darshg321/FancyBoard/pcb/Choc_Stem_MX_Size_Normal.step

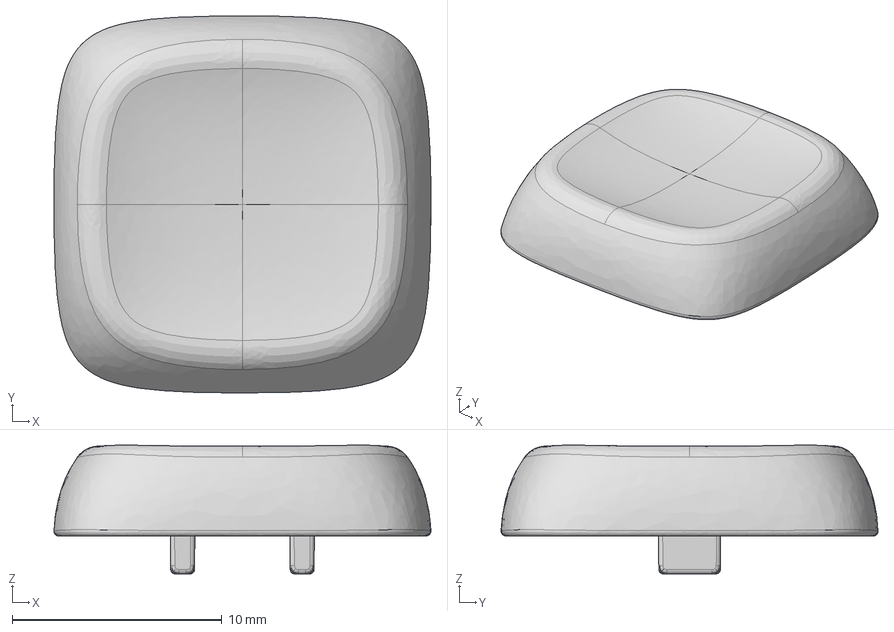
[picture p8: CAD file, 2025-07-31]
pcb/Choc_Stem_MX_Size_Normal.step
18.0 x 18.0 x 6.14 mm
