darshg321/FancyBoard/cad/draw1.dxf

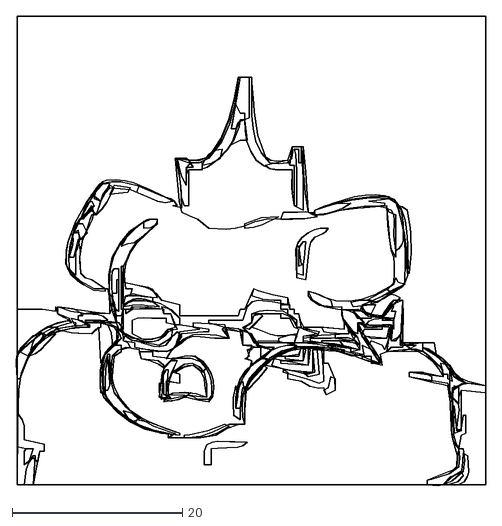
[picture p9: CAD file, 2025-08-01]
cad/draw1.dxf
55.2 x 55.1
