darshg321/FancyBoard/cad/keycaps/1.25u.SLDPRT

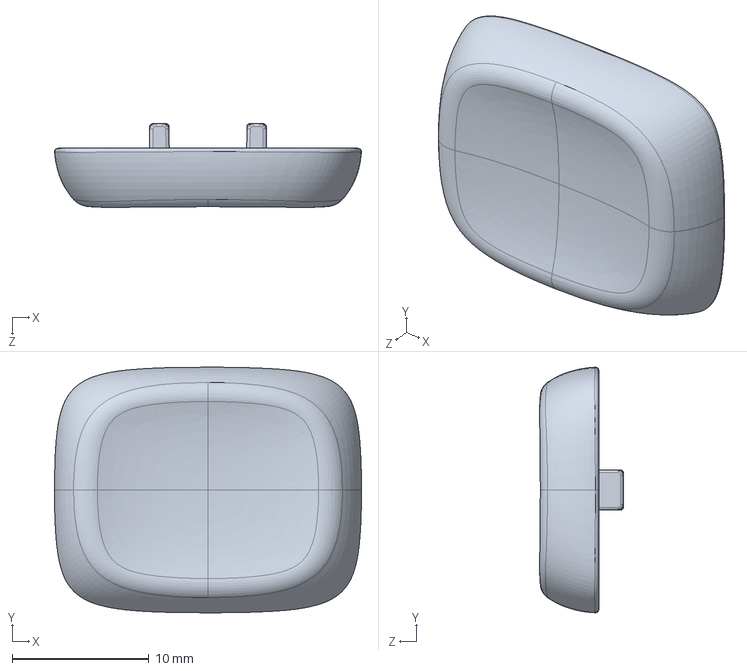
[picture p10: CAD file, 2025-08-01]
cad/keycaps/1.25u.SLDPRT
22.5 x 18.0 x 6.14 mm
