darshg321/FancyBoard/pcb/Kailh LP Choc Burnt Orange.STEP

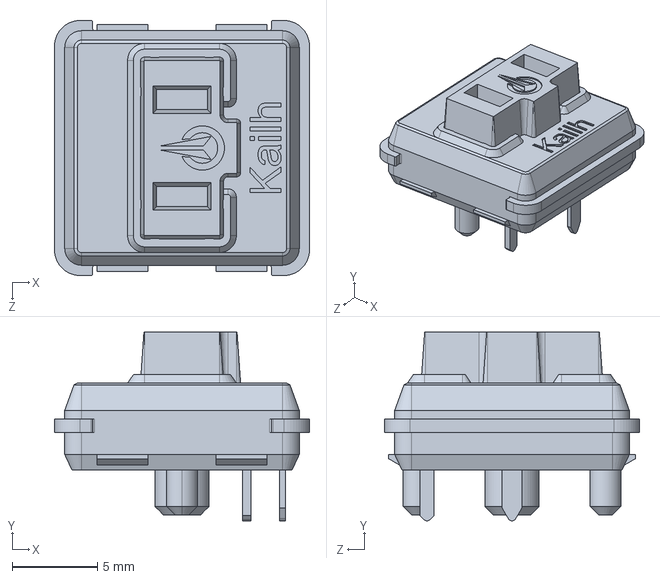
[picture p11: CAD file, 2025-07-30]
pcb/Kailh LP Choc Burnt Orange.STEP
15.0 x 11.1 x 15.0 mm
