darshg321/FancyBoard/cad/draw2.dxf

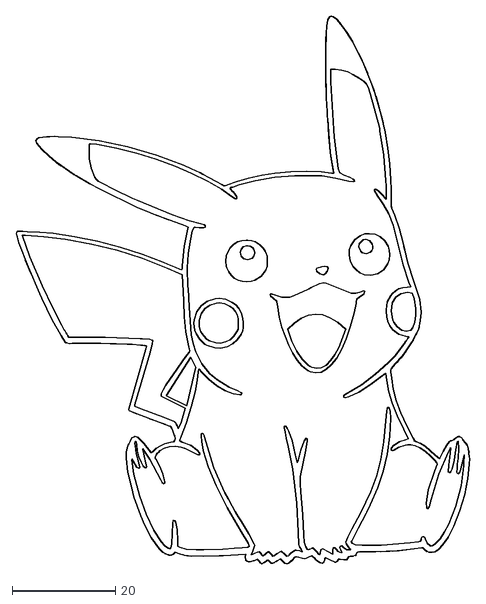
[picture p12: CAD file, 2025-08-01]
cad/draw2.dxf
87.9 x 106.2
