darshg321/FancyBoard/cad/keycaps/2.00u.SLDPRT

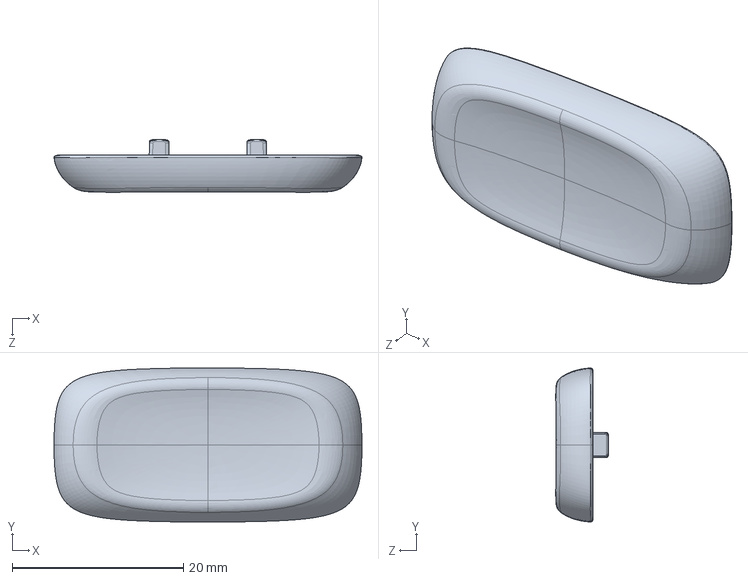
[picture p13: CAD file, 2025-08-01]
cad/keycaps/2.00u.SLDPRT
36.0 x 18.0 x 6.14 mm
