darshg321/FancyBoard/pcb/ec11.STEP

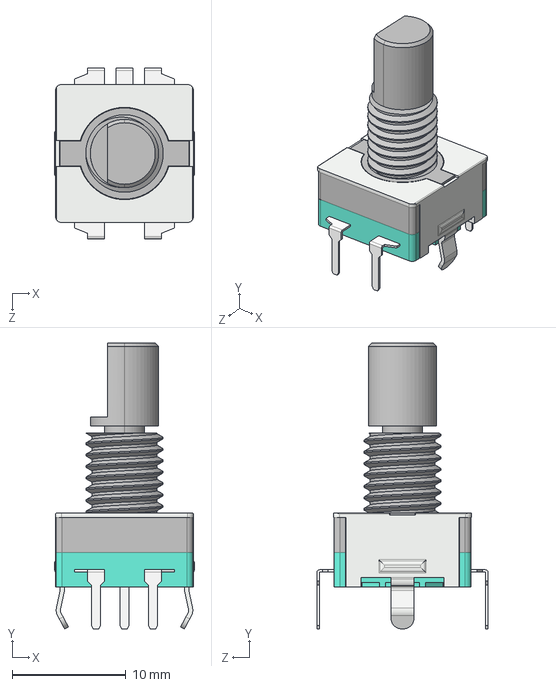
[picture p14: CAD file, 2025-07-30]
pcb/ec11.STEP
12.3 x 25.1 x 15.0 mm
