darshg321/FancyBoard/cad/keycaps/1.75.SLDPRT

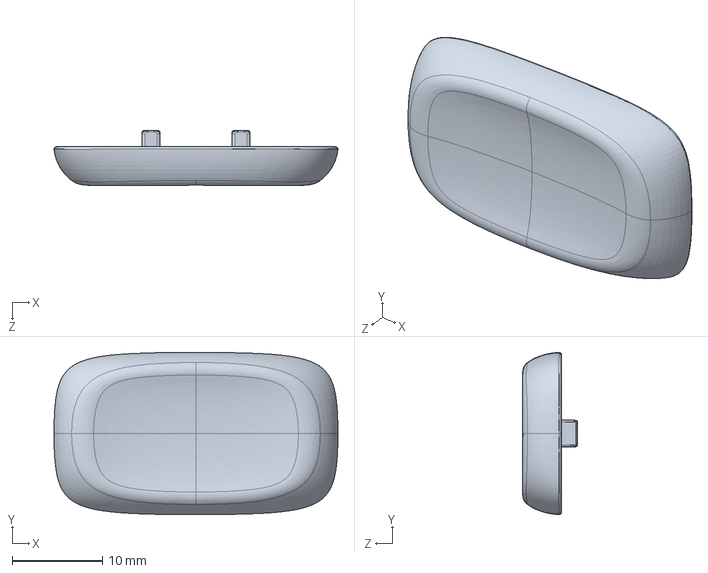
[picture p15: CAD file, 2025-08-01]
cad/keycaps/1.75.SLDPRT
31.5 x 18.0 x 6.14 mm
