darshg321/FancyBoard/cad/plate_top.dxf

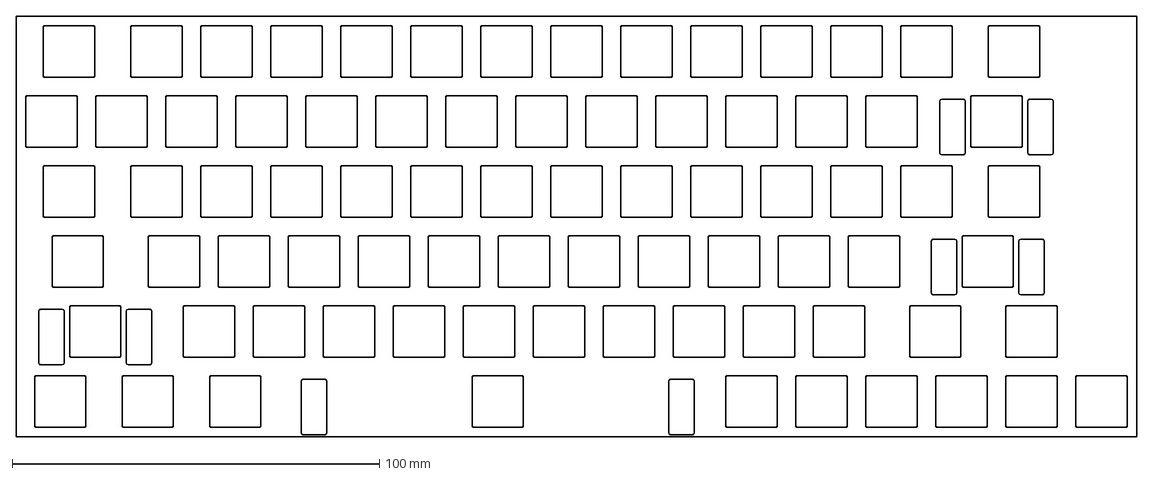
[picture p16: CAD file, 2025-07-31]
cad/plate_top.dxf
304.8 x 114.3 mm
