darshg321/FancyBoard/pcb/nice!nano v2.step

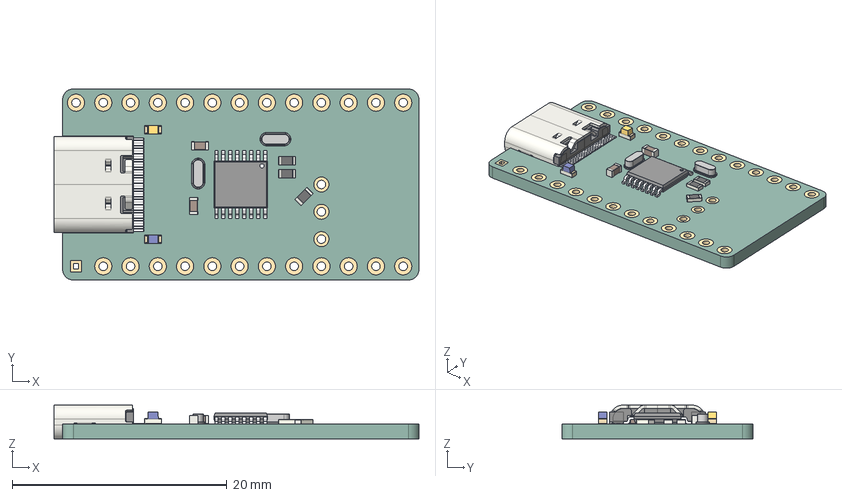
[picture p17: CAD file, 2025-07-30]
pcb/nice!nano v2.step
34.0 x 17.8 x 3.16 mm
nice!nano v1.0_1
USB_C_Receptacle_16P_TopMnt_Horizontal_GCT_USB4105-xx-A
USB_C_Receptacle_16P_TopMnt_Horizontal_GCT_USB4105-xx-A001
USB_C_Receptacle_16P_TopMnt_Horizontal_GCT_USB4105-xx-A002
USB_C_Receptacle_16P_TopMnt_Horizontal_GCT_USB4105-xx-A003
USB_C_Receptacle_16P_TopMnt_Horizontal_GCT_USB4105-xx-A004
USB_C_Receptacle_16P_TopMnt_Horizontal_GCT_USB4105-xx-A005
USB_C_Receptacle_16P_TopMnt_Horizontal_GCT_USB4105-xx-A006
USB_C_Receptacle_16P_TopMnt_Horizontal_GCT_USB4105-xx-A007
USB_C_Receptacle_16P_TopMnt_Horizontal_GCT_USB4105-xx-A008
USB_C_Receptacle_16P_TopMnt_Horizontal_GCT_USB4105-xx-A009
USB_C_Receptacle_16P_TopMnt_Horizontal_GCT_USB4105-xx-A010
USB_C_Receptacle_16P_TopMnt_Horizontal_GCT_USB4105-xx-A011
USB_C_Receptacle_16P_TopMnt_Horizontal_GCT_USB4105-xx-A012
USB_C_Receptacle_16P_TopMnt_Horizontal_GCT_USB4105-xx-A013
USB_C_Receptacle_16P_TopMnt_Horizontal_GCT_USB4105-xx-A014
USB_C_Receptacle_16P_TopMnt_Horizontal_GCT_USB4105-xx-A015
USB_C_Receptacle_16P_TopMnt_Horizontal_GCT_USB4105-xx-A016
USB_C_Receptacle_16P_TopMnt_Horizontal_GCT_USB4105-xx-A017
USB_C_Receptacle_16P_TopMnt_Horizontal_GCT_USB4105-xx-A018
USB_C_Receptacle_16P_TopMnt_Horizontal_GCT_USB4105-xx-A019
USB_C_Receptacle_16P_TopMnt_Horizontal_GCT_USB4105-xx-A020
USB_C_Receptacle_16P_TopMnt_Horizontal_GCT_USB4105-xx-A021
USB_C_Receptacle_16P_TopMnt_Horizontal_GCT_USB4105-xx-A022
USB_C_Receptacle_16P_TopMnt_Horizontal_GCT_USB4105-xx-A023
USB_C_Receptacle_16P_TopMnt_Horizontal_GCT_USB4105-xx-A024
USB_C_Receptacle_16P_TopMnt_Horizontal_GCT_USB4105-xx-A025
USB_C_Receptacle_16P_TopMnt_Horizontal_GCT_USB4105-xx-A026
USB_C_Receptacle_16P_TopMnt_Horizontal_GCT_USB4105-xx-A027
USB_C_Receptacle_16P_TopMnt_Horizontal_GCT_USB4105-xx-A028
USB_C_Receptacle_16P_TopMnt_Horizontal_GCT_USB4105-xx-A029
USB_C_Receptacle_16P_TopMnt_Horizontal_GCT_USB4105-xx-A030
USB_C_Receptacle_16P_TopMnt_Horizontal_GCT_USB4105-xx-A031
USB_C_Receptacle_16P_TopMnt_Horizontal_GCT_USB4105-xx-A032
USB_C_Receptacle_16P_TopMnt_Horizontal_GCT_USB4105-xx-A033
USB_C_Receptacle_16P_TopMnt_Horizontal_GCT_USB4105-xx-A034
USB_C_Receptacle_16P_TopMnt_Horizontal_GCT_USB4105-xx-A035
Pin9
Pin10
Pin12
Pin11
Pin13
Pin14
Pin15
Pin16
Pin8
Pin7
Pin6
Pin5
Pin4
Pin3
Pin2
Pin1
LED_0603_1608Metric_ON
C_0603_1608Metric x 2
LED_0603_1608Metric_ON_1
Crystal Oscillator x 2
R_0603_1608Metric x 4
