darshg321/FancyBoard/cad/keycaps/6.25u.SLDPRT

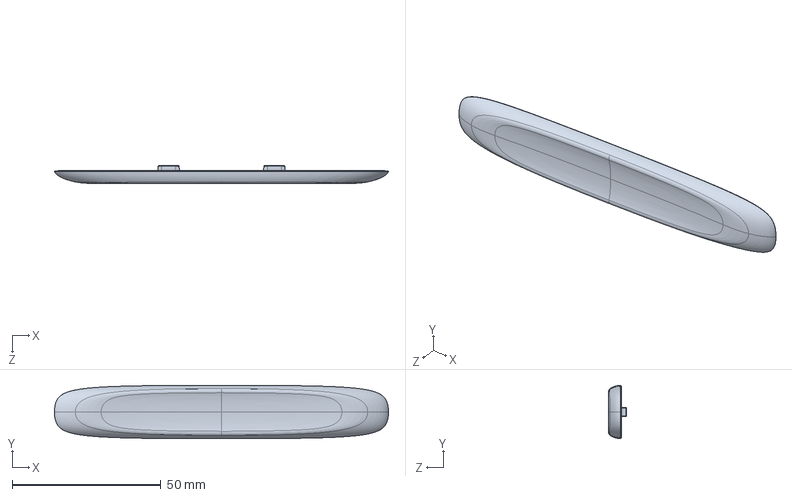
[picture p18: CAD file, 2025-08-01]
cad/keycaps/6.25u.SLDPRT
112.4 x 18.0 x 6.14 mm
